russell-davis/Retro-Deck/docs/README.md

# Retro Deck — Docs

Design history and specifications. The V2 rewrite is **merged to `main`**; the
slice PRDs below are kept as the record of how it was built, not as open work.

| Doc | What it is | Status |
|-----|---|---|
| [V2_PRD.md](V2_PRD.md) | Primary V2 product spec — architecture, protocol, API, config schema | **Source of truth** |
| [V2_ISSUES.md](V2_ISSUES.md) | The 17 scoped implementation issues derived from the PRD | Mostly delivered |
| [V2_REWRITE_ANALYSIS.md](V2_REWRITE_ANALYSIS.md) | Snapshot/analysis of the V1 firmware that motivated the rewrite | Historical |
| [HANDOFF.md](HANDOFF.md) | Original V2 kickoff brief (open questions, decisions) | Historical |
| [V2_SLICE2_PRD.md](V2_SLICE2_PRD.md) | Slice 2 — binding editor + keypress dispatch | Done |
| [V2_SLICE3_PRD.md](V2_SLICE3_PRD.md) | Slice 3 — action results + profile CRUD | Done |
| [V2_SLICE4_PRD.md](V2_SLICE4_PRD.md) | Slice 4 — profile-cycle action + hold-slot editor | Done |
| [V2_SLICE5_PRD.md](V2_SLICE5_PRD.md) | Slice 5 — reliability (keyboard hijack) + diagnostics | **In progress** |

User-facing setup and bill-of-materials live in the root [`README.md`](../README.md).
